OLIMEX/USB-4SERIAL/HARDWARE/USB-4SERIAL_Rev_B/3d/70054376.stp

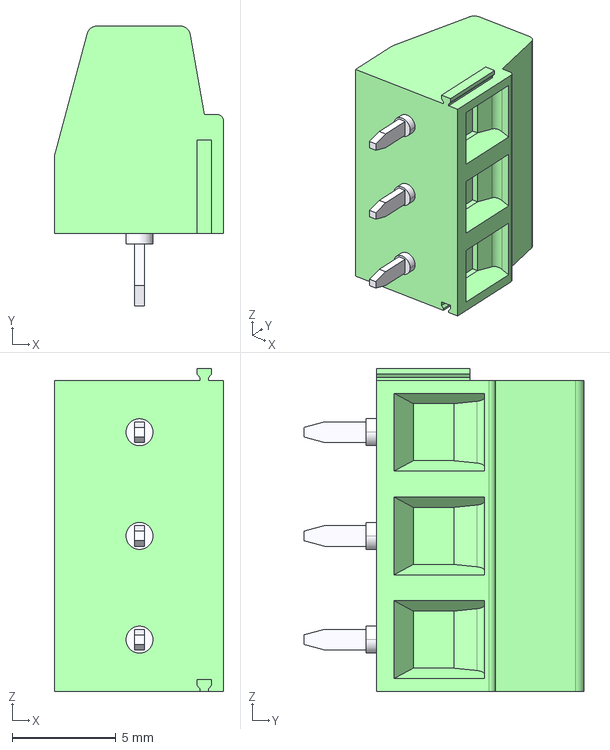
[picture p19: CAD file, 2023-05-23]
HARDWARE/USB-4SERIAL_Rev_B/3d/70054376.stp
8.15 x 13.5 x 15.6 mm
